avadsariya0-coder/USB-HUB/IMAGES/front.png

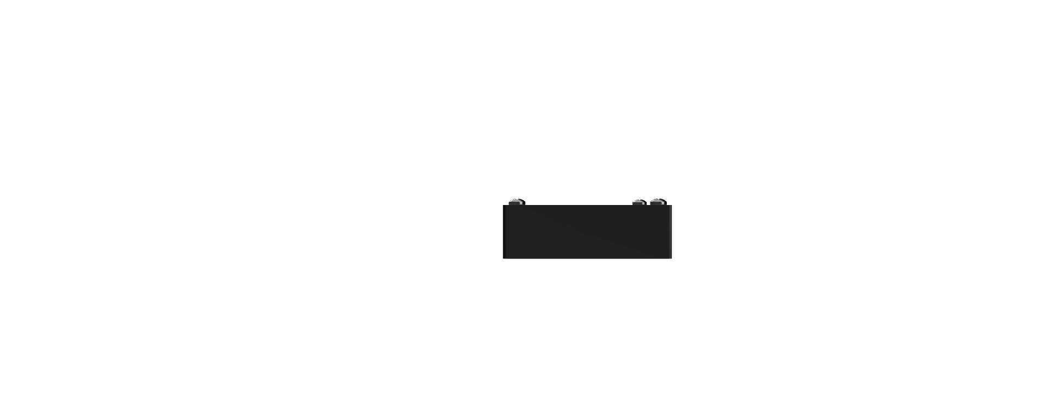
IMAGES/front.png
