avadsariya0-coder/USB-HUB/IMAGES/P.C.B.png

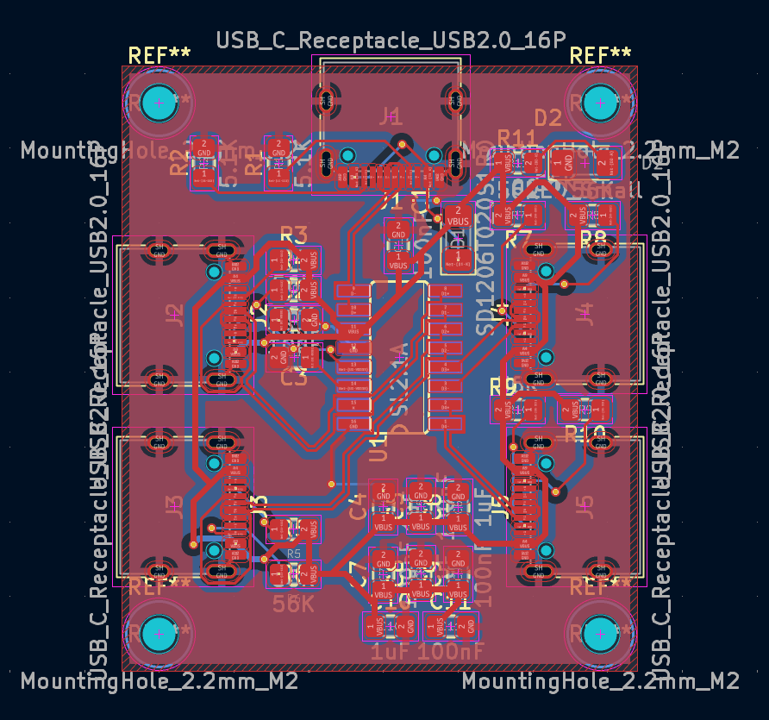
IMAGES/P.C.B.png
